Christian-ALLEGRE/CommutAntennes/images/20230911_130225.jpg

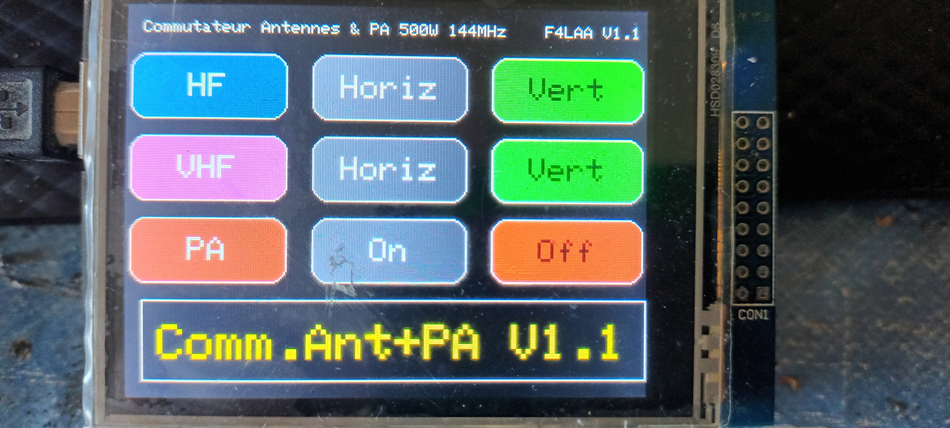
images/20230911_130225.jpg
