Christian-ALLEGRE/CommutAntennes/images/20231004_191355.jpg

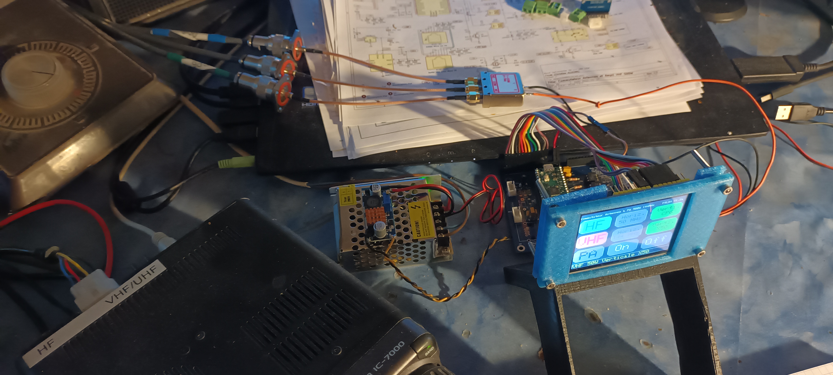
images/20231004_191355.jpg
