Christian-ALLEGRE/CommutAntennes/images/20231006_193105.jpg

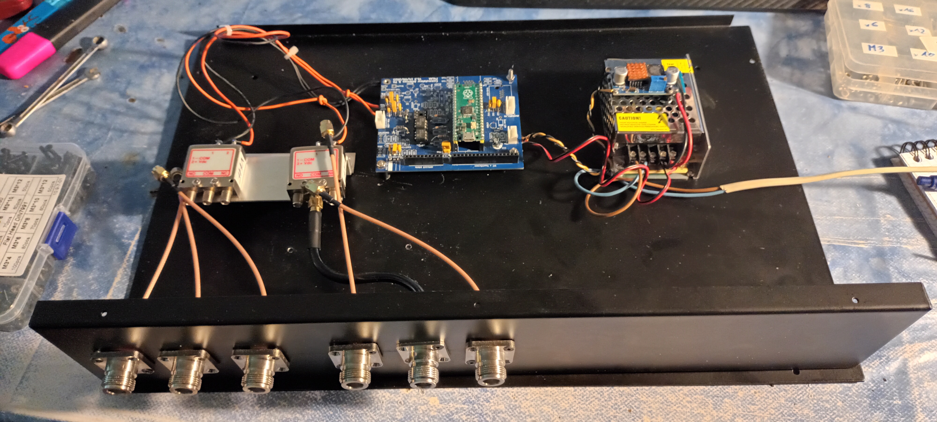
images/20231006_193105.jpg
