Christian-ALLEGRE/CommutAntennes/images/20231006_193206.jpg

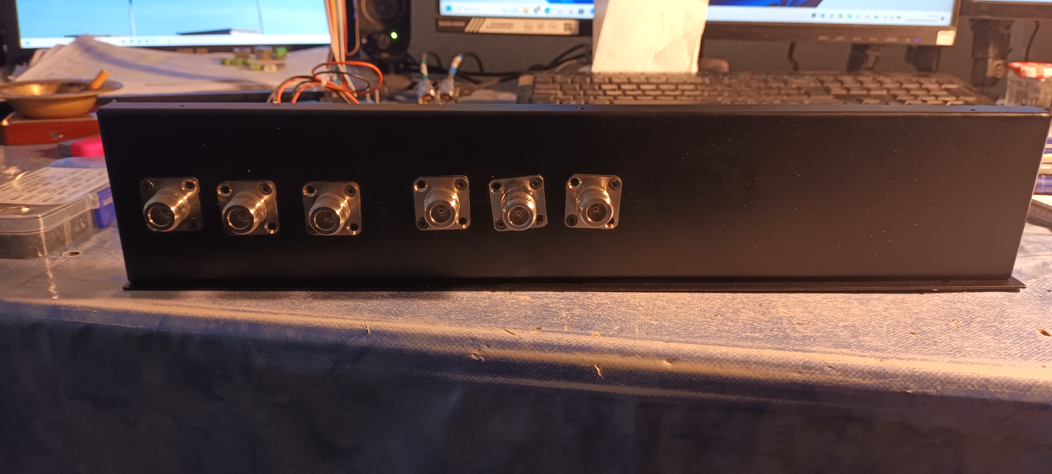
images/20231006_193206.jpg
