Christian-ALLEGRE/CommutAntennes/images/20231007_115457.jpg

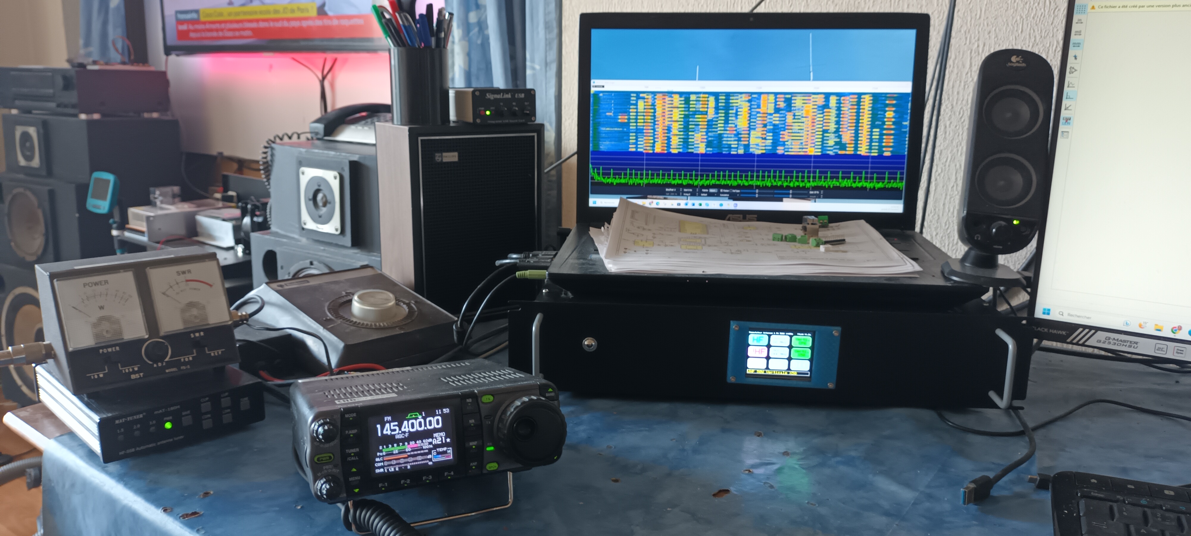
images/20231007_115457.jpg
