Christian-ALLEGRE/CommutAntennes/images/20231007_152153.jpg

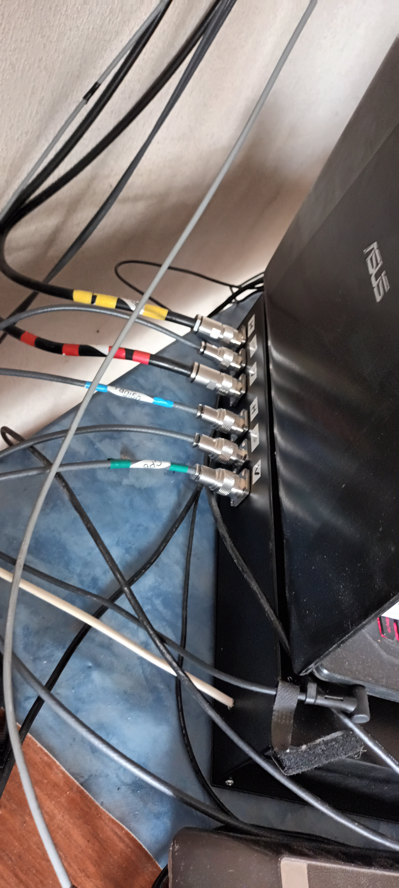
images/20231007_152153.jpg
